gerb-ster/Curstis-VCO/images/20190215_065219.png

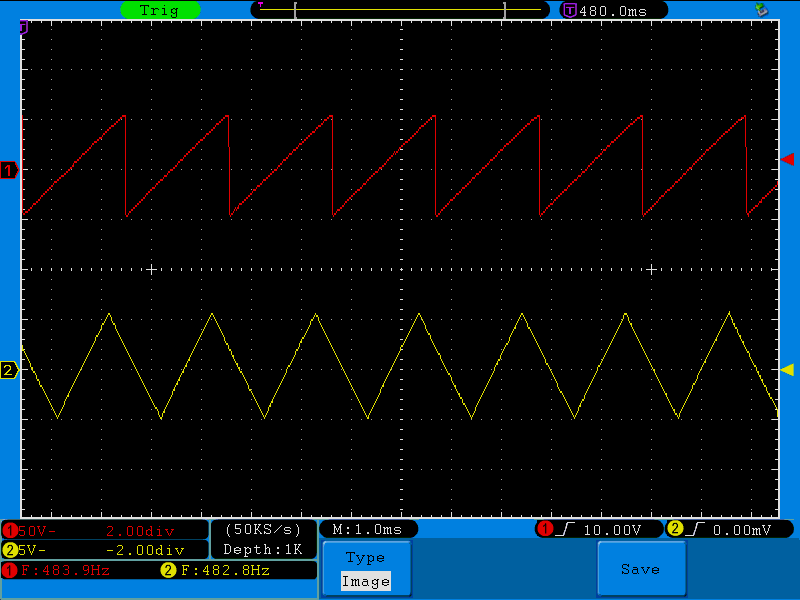
images/20190215_065219.png
