gerb-ster/Curstis-VCO/images/20190215_065245.png

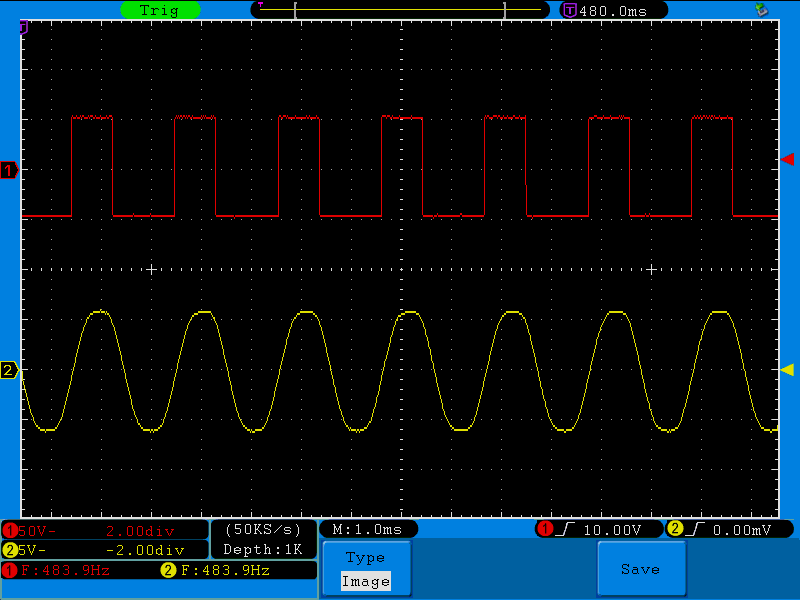
images/20190215_065245.png
