gerb-ster/Curstis-VCO/images/20190215_065304.png

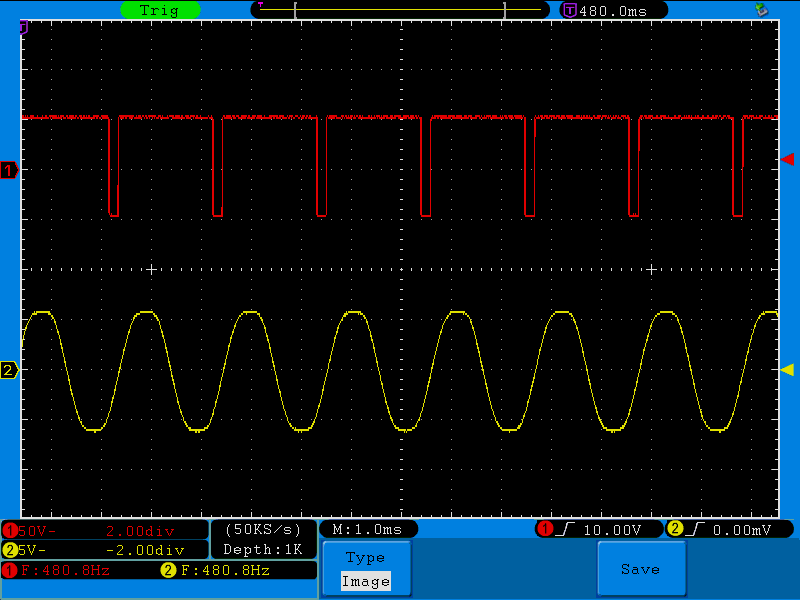
images/20190215_065304.png
